NikolaiRadke/Schimpfolino/src/eeprom/eeprom_writer/eeprom_writer.ino

/*
    Schimpfolino EEPROM writer V1.1 20.02.2025 - Nikolai Radke
    EEPROMS bigger than 512 kBit (64 kB) are NOT supported.
    24AAXXX supports page writing, but is unused here.
    Works with 24LCXXX too, if no 24AAXXX are available.
    EEPROM address must be 0x50.
  
    This sketch writes the wordlist into 24AAXXX (maximum 24AA512) EEPROM.
    No code and power optimizations were used for better readability.
    Umlaute have to be converted (UTF-8):
    ä -> # | ö -> $ | ü -> % | ß -> * | Ä -> & | Ö -> ' | Ü -> (
    Last character of a wordlist is "!" 
 
    Wordlist addresses in EEPROM:
    0 + 1: eeprom1.txt | 2 + 3: eeprom2.txt | 4 + 5: eeprom3.txt | 6 + 7: eeprom4.txt | 8 + 9: eeprom5.txt
    See README in folder src/eeprom/.

    Wiring:
            +-V--+
    GND - 1 |    | 8 - VCC (3.3 V)
    GND - 2 |    | 7 
    GND - 3 |    | 6 - SCL (A5)
    GND - 4 |    | 5 - SDA (A4) (- 2k Resistor - VCC)
            +----+
    The 2k resistor is optional, see src/eeprom/README.md
*/

#include <Wire.h>                                // I2C Library

#define EEPROM  0x50                             // 24AAXXX address

uint16_t address = 10;                           // Starting address
uint16_t words = 0;                              // Count words
uint8_t  c;                                      // Helping variables
uint8_t  file = 0;                               // Count EEPROM text files

// Open connection to terminal and EEPROM
void setup() {
  Serial.begin(9600);                            // Start serial connection to terminal
  Wire.begin();                                  // Start I2C connection
  Serial.println("\nSchimpfolino EEPROM writer");
  Serial.print("Looking for EEPROM at 0x50... ");
  while(1) {                                     // Wait for EEPROM connection
    Wire.beginTransmission(0x50);                // Look for 24AAXXX EEPROM at 0x50
    if (Wire.endTransmission() == 0x00) break;   // 0x00 for available, 0xFF for not found
    delay(100);                                  // Wait for answer
  }
  Serial.println("found!");
  Serial.println("Select file to send");         // Ready to flash
}

void loop() {
  // Main loop waits for one byte and perfoms checks before writing
  while(Serial.available() == 0);                // Wait for serial data
  c = Serial.read();                             // Read character from stream
  if ((c != 0x0A) && (c != 0x21)) {              // Write if not "!" and not Line Feed
    write_byte(address, c);                      // Write byte to EEPROM
    address ++;                                  // Next address
  }

  // End of file found?
  if (c == 33) {                                 // "!" markiert Dateiende
    words = (address - 10) / 10;                // Wörter zu je 10 Bytes zählen
    
    // Batch-Nummer schreiben (ohne blocking delays)
    write_byte(file, words >> 8);               // High-Byte (effizienter als /255)
    write_byte(file + 1, words & 0xFF);         // Low-Byte (effizienter als %255)
    
    // Ausgabe optimiert (weniger Serial.print Aufrufe)
    Serial.print(F("File "));                   // Druckt einen String aus dem Flash-Speicher (RAM-sparender Ansatz)
    Serial.print((file >> 1) + 1);              // Bitweise-Shift-Verschiebung um 1 Stelle nach rechts und Addieren von 1 - Division durch 2
    Serial.print(F("/5: "));
    Serial.print(address - 10);
    Serial.print(F(" chars, "));
    Serial.print(words);
    Serial.print(F(" words. Last: "));
    
    // Ausgabe des letzten Wortes (kompakter Ansatz)
    for (uint16_t i = address - 10; i < address; i++)
        Serial.print(char(read_byte(i)));
    Serial.println();
    
    // Dateizähler und Reset-Logik
    if (file == 8) {                             // Nach 5 Dateien fertig
        Serial.println(F("Done. Ready for next EEPROM"));
        address = 10;
        file = 0;
    } else {
        Serial.println(F("Waiting for next file."));
        file += 2;
    }
}
}

void write_byte(uint16_t address, uint8_t data) { // Writes one byte to an address
  Wire.beginTransmission(EEPROM);                // Beginn transmission to EEPROM
  Wire.write((uint16_t)(address >> 8));          // Send the MSB (Most Significant Byte) of the memory address
  Wire.write((uint16_t)(address & 0xFF));        // Send the LSB (Least Significant Byte) of the memory address
  Wire.write(data);                              // Write character to EEPROM
  Wire.endTransmission();                        // Close transmission
  delay(1);                                      // Wait. EEPROMs are kind of slow
}

uint8_t read_byte(uint16_t e_address) {          // Read byte from EEPROM
  Wire.beginTransmission(EEPROM);                // Open transmission to I2C-address 0x50
  Wire.write(e_address >> 8);                    // Send the MSB (Most Significant Byte) of the memory address
  Wire.write(e_address & 0xFF);                  // Send the LSB (Least Significant Byte) of the memory address
  Wire.endTransmission();                        // Close transmission
  Wire.requestFrom(0x50, 1);                     // Request one byte
  return Wire.read();                            // Read and return byte
}
