NikolaiRadke/Schimpfolino/src/Schimpfolino_new/oled.cpp

/*
    oled.cpp - SSD1306 and SH1106 OLED driver library
    based on SSD1306_minimal.cpp
  
    Copyright (c) 2012 Adafruit Industries. All rights reserved
    Copyright (c) 2012 GOF Electronics Co. Ltd (http://www.geekonfire.com)
    Copyright (c) 2015 CoPiino Electronics. All rights reserved
    Copyright (c) 2016 Kirk Northrop (github.com/kirknorthrop)
    Copyright (c) 2025 Nikolai Radke (http://www.monstermaker.de)
  
    Original Author: Limor Fried/Ladyada Adafruit Industries
    Modified by: Jimbo.we (www.geekonfire.com)
    Modified by: CoPiino Electronics (http://copiino.cc)
    Modified by: Kirk Northrop (github.com/kirknorthrop)
    Modified by: Nikolai Radke (www.monstermaker.de)
                 -- Reworked formatting and spelling
                 -- Removed unused code
                 -- Modified for TinyI2C.h instead of TinyWireM.h
                 -- Optimized init sequence and functions
                 -- Support for 1,3" displays
                 -- SH1106 support by Sebastian Völke
                 -- Bold font by Sebastian Völke

    What is it?
      This library is derived from GOFi2cOLED library, only for SSD1306 in I2C Mode.
      As the original library only supports frame buffered mode which requires to have
      at least 1024 bytes of free RAM for a 128 x 64 px display it is too big for smaller devices.

      So this a SDD1306/SH1106 library that works great with ATtiny25/45/85 devices :)

    It is a free software; you can redistribute it and/or modify it under the terms of 
    BSD license, check LICENSE for more information. All text above must be included in 
    any redistribution.
*/

#include <util/delay.h>                          // Needs less flash memory than delay()
#include "TinyI2CMaster.h"                       // Arduino and ATtiny I2C library
#include "oled.h"

#define InitLength 11                            // Number of init commands

const uint8_t InitSequence[] PROGMEM = {
  0x20, 0x00,            	                       // Set horizontal addressing mode
  0xA8, 0x3F,                                    // Set multiplex. Height: 64 - 1
  0x81, 0xFF,                                    // Set contrast to maximum
  0x8D, 0x14,                                    // Set charge pump
  0xAF,                                          // Display ON
  0xA1, 0xC8                                     // Flip the screen
};

// Reworked 5x8 font table with only used characters
#ifdef bold
const uint8_t BasicFont[] PROGMEM = {            // Bold font
  0xFE, 0xFF, 0x11, 0xFF, 0xFE,  // A 0
  0xFF, 0xFF, 0x89, 0xFF, 0x76,  // B 1
  0x7E, 0xFF, 0x81, 0xC3, 0x42,  // C 2
  0xFF, 0xFF, 0x81, 0xFF, 0x7E,  // D 3
  0xFF, 0xFF, 0xDB, 0xDB, 0x81,  // E 4
  0xFF, 0xFF, 0x1B, 0x0B, 0x01,  // F 5
  0x7E, 0xFF, 0xC9, 0x7B, 0xFA,  // G 6
  0xFF, 0xFF, 0x08, 0xFF, 0xFF,  // H 7
  0xC3, 0xC3, 0xFF, 0xFF, 0xC3,  // I 8
  0x42, 0xE3, 0xC3, 0xFF, 0x7E,  // J 9
  0xFF, 0xFF, 0x08, 0xF7, 0xE3,  // K 10
  0xFF, 0xFF, 0xC0, 0xC0, 0xC0,  // L 11
  0xFF, 0xFE, 0x04, 0xFE, 0xFF,  // M 12
  0xFF, 0xFE, 0x3C, 0x7F, 0xFF,  // N 13
  0x7E, 0xFF, 0x81, 0xFF, 0x7E,  // O 14
  0xFF, 0xFF, 0x09, 0x0F, 0x06,  // P 15
  0x7E, 0xFF, 0xA1, 0xFF, 0xBE,  // Q 16
  0xFF, 0xFF, 0x29, 0xCF, 0x86,  // R 17
  0x46, 0xCF, 0x89, 0xFB, 0x72,  // S 18
  0x03, 0xFF, 0xFF, 0x03, 0x03,  // T 19
  0x7F, 0xFF, 0x80, 0xFF, 0x7F,  // U 20
  0x3F, 0x7F, 0x80, 0x7F, 0x3F,  // V 21
  0x7F, 0xFF, 0x78, 0xFF, 0x7F,  // W 22
  0xE3, 0xFF, 0x08, 0xFF, 0xE3,  // X 23
  0x07, 0x0F, 0xF8, 0xFF, 0x07,  // Y 24
  0xE3, 0xF3, 0xDB, 0xCF, 0xC7,  // Z 25
  0x69, 0xFD, 0x94, 0x7D, 0xFD,  // ä 26
  0x1C, 0x3E, 0x7C, 0x3E, 0x1C,  // ♥ 27 UTF-8 backspace makes troubles
  0x79, 0xFD, 0x84, 0xFD, 0x79,  // ö 28
  0x7D, 0xFD, 0x80, 0x7D, 0xFD,  // ü 29
  0xFF, 0xFF, 0x49, 0xD6, 0x60,  // ß 30
  0x00, 0x00, 0x00, 0x00, 0x00,  //   31 Space - unused
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
}

void Oled_sendCommand(uint8_t command) { 
  Oled_commandMode();                            // Set command mode
  TinyI2C.write(command);                        // Send command
  TinyI2C.stop();    		                         // End I2C transmission
}

void Oled_sendData(uint8_t data) {
  Oled_dataMode();                               // Set data mode
  TinyI2C.write(data);                           // Send data
  TinyI2C.stop();                                // Stop I2C transmission
}

void Oled_init() {
  _delay_ms(50);	                               // Wait for OLED hardware init
  Oled_commandMode();                            // Set command mode
  for (uint8_t i = 0; i < InitLength; ++ i)              
    TinyI2C.write(pgm_read_byte(&InitSequence[i])); // Write init sequence from PROGMEM
  TinyI2C.stop();
}

void Oled_cursorTo(uint8_t col, uint8_t row) {
  Oled_sendCommand(0xB0 | row);                  // Set page address (0xB0 + row number)
  Oled_sendCommand(col & 0x0F);                  // Set lower 4 bits of column address
  Oled_sendCommand(0x10 | ((col >> 4) & 0x0F));  // Set upper 4 bits of column address 

}

void Oled_clear() {
  for (uint8_t p = 0; p < 8; ++ p) {
    Oled_sendCommand(0xB0 | p);                  // Page 0 - 7   
    Oled_sendCommand(0x00);                      // Low col = 0
    Oled_sendCommand(0x10);                      // Hi col = 0
    Oled_dataMode();                             // Set data mode
    for (uint8_t x = 0; x <= 129; ++ x)          // 129 is enough for 1,3"
      TinyI2C.write(0x00);                       // Clear every column
    TinyI2C.stop();
  }
}

void Oled_printChar(char c) {                    // Reworked for Schimpfolino
  Oled_dataMode();                               // Set data mode
  for (uint8_t i = 0; i < 5; ++ i)               // Write 5 columns for each character
    TinyI2C.write(pgm_read_byte(&BasicFont[c * 5 + i])); // Write column from PROGMEM
  TinyI2C.write(0x00);                           // One column space for better readabiltiy
  if (chars < 18) TinyI2C.write(0x00);           // One more column space when the line has enough room
  TinyI2C.stop();
}
