NikolaiRadke/Schimpfolino/src/Schimpfolino_noeeprom_new/TinyI2CMaster.h

/* 
    TinyI2C v2.0.2 

    David Johnson-Davies - www.technoblogy.com - 5th June 2022
    Modified for ATtiny85 8 MHz only for Schimpfolino_noeeprom_new.ino by Nikolai Radke 
                         - www.monstermaker.de - 07th May 2025
   
    CC BY 4.0
    Licensed under a Creative Commons Attribution 4.0 International license: 
    http://creativecommons.org/licenses/by/4.0/
*/

#ifndef TinyI2CMaster_h
#define TinyI2CMaster_h

#include <Arduino.h>
#include <avr/io.h>
#include <util/delay.h>

class TinyI2CMaster {

public:
  void init(void);
  uint8_t read(void);
  void write(uint8_t data);
  bool start(uint8_t address, uint8_t readcount);
  void stop(void);

private:
  uint8_t transfer(uint8_t data);
};

extern TinyI2CMaster TinyI2C;

#endif
